arunkhanna00/FMCW_radar/code/dwfconstants.py

from ctypes import *

#HDWF
hdwfNone = c_int(0)

#ENUMFILTER
enumfilterAll       = c_int(0)
enumfilterEExplorer = c_int(1)
enumfilterDiscovery = c_int(2)

#DEVID
devidEExplorer  = c_int(1)
devidDiscovery  = c_int(2)

#DEVVER
devverEExplorerC   = c_int(2)
devverEExplorerE   = c_int(4)
devverEExplorerF   = c_int(5)
devverDiscoveryA   = c_int(1)
devverDiscoveryB   = c_int(2)
devverDiscoveryC   = c_int(3)

#TRIGSRC
trigsrcNone                 = c_byte(0)
trigsrcPC                   = c_byte(1)
trigsrcDetectorAnalogIn     = c_byte(2)
trigsrcDetectorDigitalIn    = c_byte(3)
trigsrcAnalogIn             = c_byte(4)
trigsrcDigitalIn            = c_byte(5)
trigsrcDigitalOut           = c_byte(6)
trigsrcAnalogOut1           = c_byte(7)
trigsrcAnalogOut2           = c_byte(8)
trigsrcAnalogOut3           = c_byte(9)
trigsrcAnalogOut4           = c_byte(10)
trigsrcExternal1            = c_byte(11)
trigsrcExternal2            = c_byte(12)
trigsrcExternal3            = c_byte(13)
trigsrcExternal4            = c_byte(14)

# instrument states
DwfStateReady        = c_byte(0)
DwfStateConfig       = c_byte(4)
DwfStatePrefill      = c_byte(5)
DwfStateArmed        = c_byte(1)
DwfStateWait         = c_byte(7)
DwfStateTriggered    = c_byte(3)
DwfStateRunning      = c_byte(3)
DwfStateDone         = c_byte(2)

#STS
stsRdy		= c_byte(0)
stsArm		= c_byte(1)
stsDone		= c_byte(2)
stsTrig		= c_byte(3)
stsCfg		= c_byte(4)
stsPrefill	= c_byte(5)
stsNotDone	= c_byte(6)
stsTrigDly	= c_byte(7)
stsError	= c_byte(8)
stsBusy		= c_byte(9)
stsStop		= c_byte(10)

#ACQMODE
acqmodeSingle       = c_int(0)
acqmodeScanShift    = c_int(1)
acqmodeScanScreen   = c_int(2)
acqmodeRecord       = c_int(3)

#FILTER
filterDecimate = c_int(0)
filterAverage  = c_int(1)
filterMinMax   = c_int(2)

#TRIGTYPE
trigtypeEdge         = c_int(0)
trigtypePulse        = c_int(1)
trigtypeTransition   = c_int(2)

#TRIGCOND;
trigcondRisingPositive   = c_int(0)
trigcondFallingNegative  = c_int(1)

#TRIGLEN;
triglenLess       = c_int(0)
triglenTimeout    = c_int(1)
triglenMore       = c_int(2)

#DWFERC;                           
dwfercNoErc                  = c_int(0)		#  No error occurred
dwfercUnknownError           = c_int(1)		#  API waiting on pending API timed out
dwfercApiLockTimeout         = c_int(2)		#  API waiting on pending API timed out
dwfercAlreadyOpened          = c_int(3)		#  Device already opened
dwfercNotSupported           = c_int(4)		#  Device not supported
dwfercInvalidParameter0      = c_int(16)	#  Invalid parameter sent in API call
dwfercInvalidParameter1      = c_int(17)	#  Invalid parameter sent in API call
dwfercInvalidParameter2      = c_int(18)	#  Invalid parameter sent in API call
dwfercInvalidParameter3      = c_int(19)	#  Invalid parameter sent in API call

#FUNC;
funcDC       = c_byte(0)
funcSine     = c_byte(1)
funcSquare   = c_byte(2)
funcTriangle = c_byte(3)
funcRampUp   = c_byte(4)
funcRampDown = c_byte(5)
funcNoise    = c_byte(6)
funcCustom   = c_byte(30)
funcPlay     = c_byte(31)

#ANALOGIO;
analogioEnable      = c_byte(1)
analogioVoltage     = c_byte(2)
analogioCurrent     = c_byte(3)
analogioPower       = c_byte(4)
analogioTemperature	= c_byte(5)

AnalogOutNodeCarrier  = c_int(0)
AnalogOutNodeFM       = c_int(1)
AnalogOutNodeAM       = c_int(2)

DwfDigitalInClockSourceInternal = c_int(0)
DwfDigitalInClockSourceExternal = c_int(1)

DwfDigitalInSampleModeSimple   = c_int(0)
# alternate samples: noise|sample|noise|sample|...  
# where noise is more than 1 transition between 2 samples
DwfDigitalInSampleModeNoise    = c_int(1)

DwfDigitalOutOutputPushPull   = c_int(0)
DwfDigitalOutOutputOpenDrain  = c_int(1)
DwfDigitalOutOutputOpenSource = c_int(2)
DwfDigitalOutOutputThreeState = c_int(3) 

DwfDigitalOutTypePulse      = c_int(0)
DwfDigitalOutTypeCustom     = c_int(1)
DwfDigitalOutTypeRandom     = c_int(2)

DwfDigitalOutIdleInit     = c_int(0)
DwfDigitalOutIdleLow      = c_int(1)
DwfDigitalOutIdleHigh     = c_int(2)
DwfDigitalOutIdleZet      = c_int(3)
